CREATE-ROCKET/Avi_89J_Pitot_log/main/src/interfaces/flash.h

#ifndef _spi_flash_
#define _spi_flash_

namespace flash
{
    int init();
    void writeDataToFlash(void *pvParameter);
    void eraseFlash();
    void writeFlashDataToSD(void *pvParameter);
}

#endif
