CREATE-ROCKET/Avi_89J_Pitot_log/main/src/interfaces/SD_fast.h

#ifndef _sd_fast_
#define _sd_fast_

namespace sd_mmc
{
    // setup
    int init();
    int makeNewFile();
    // makeParity
    void makeParity(void *pvParameter);
    // write
    void writeDataToSD(void *pvParameter);
    // close task(interrupt)
    void onButton();
}

#endif
